Udushu/smoke-mate-9002/images/smokemate_front_left.png

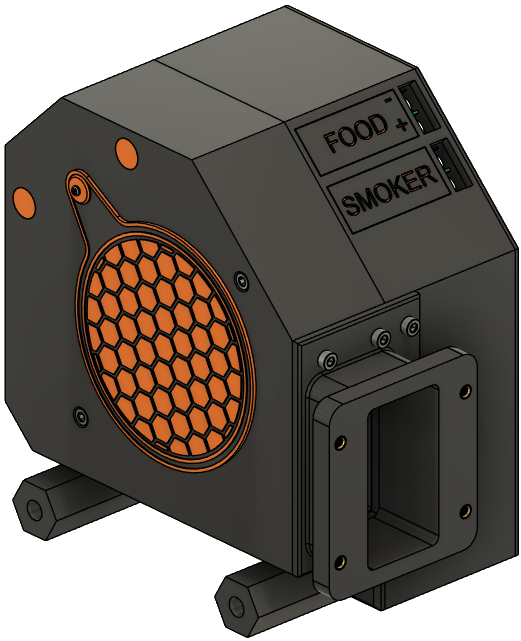
images/smokemate_front_left.png
