Udushu/smoke-mate-9002/images/smokemate_front_left_no_damper.png

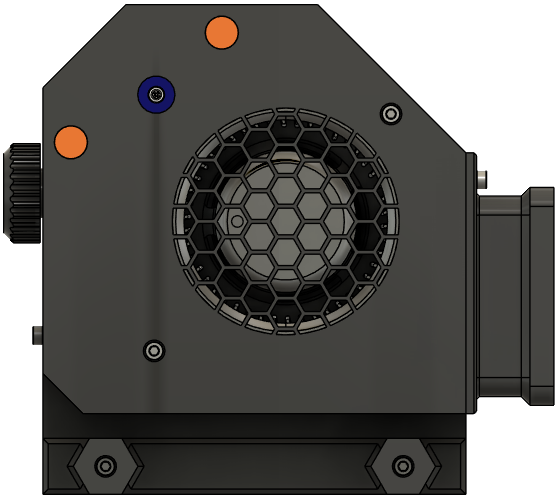
images/smokemate_front_left_no_damper.png
