Udushu/smoke-mate-9002/images/smokemate_front_right.png

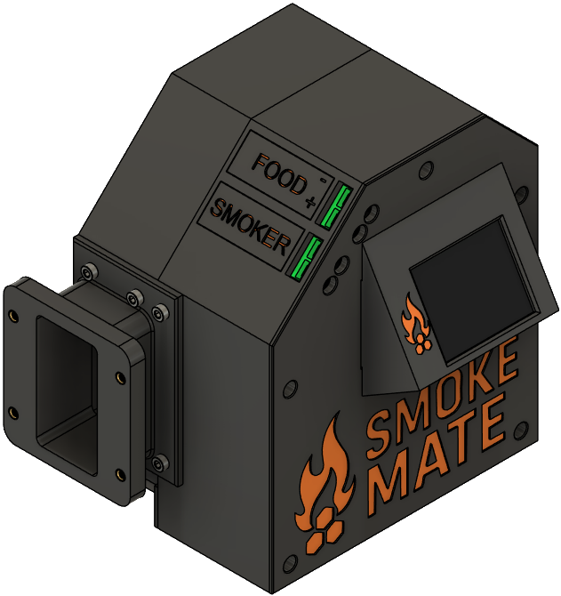
images/smokemate_front_right.png
