Udushu/smoke-mate-9002/images/smokemate_left_no_fan_housing.png

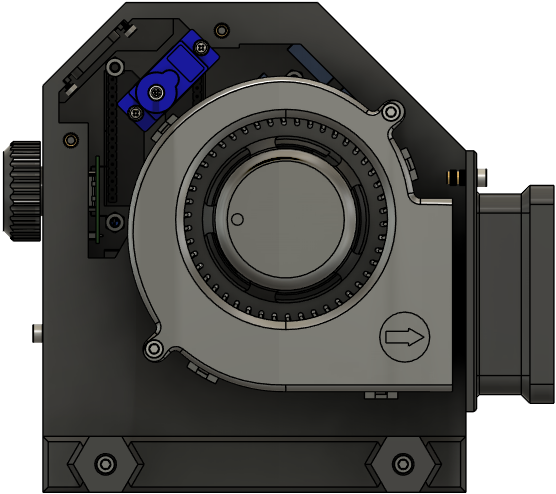
images/smokemate_left_no_fan_housing.png
